bitbank2/CO2_USB_033/User/Open_Sans_Condensed_Bold_24.h

// Created by http://oleddisplay.squix.ch/ Consider a donation
// In case of problems make sure that you are using the font file with the correct version!
const uint8_t Open_Sans_Condensed_Bold_24Bitmaps[] PROGMEM = {

	// Bitmap Data:
	0x00, // ' '
	0x77,0x77,0x77,0x77,0x77,0x70,0x07,0xFF,0x70, // '!'
	0xE7,0x63,0x63,0x63,0x63,0x63, // '"'
	0x0E,0x60,0x63,0x03,0x38,0x19,0xC0,0xCC,0x3F,0xFD,0xFF,0xE3,0x98,0x18,0xC0,0xCE,0x3F,0xFD,0xFF,0xE1,0x98,0x1C,0xC0,0xE6,0x06,0x30,0x33,0x80, // '#'
	0x08,0x04,0x0F,0x8F,0xFF,0xF7,0x4B,0xA1,0xD0,0x78,0x1F,0x03,0xC1,0x70,0xBC,0x5F,0xFF,0xFE,0x7E,0x04,0x02,0x00, // '$'
	0x78,0x30,0xFC,0x30,0xEC,0x70,0xCC,0x60,0xCC,0xE0,0xCE,0xC0,0xCC,0xDE,0xCD,0xFE,0xED,0xB7,0xFF,0xB3,0x7B,0x73,0x03,0x73,0x07,0x73,0x06,0x33,0x0E,0x37,0x0C,0x3E,0x1C,0x1C, // '%'
	0x1E,0x01,0xFC,0x1F,0xE0,0xE7,0x07,0x38,0x3D,0xC0,0xFC,0x03,0xC0,0x7E,0x33,0xF3,0xB9,0xDD,0xCF,0xEE,0x3E,0x70,0xF3,0xFF,0x8F,0xFE,0x3E,0x70, // '&'
	0xE6,0x66,0x66, // '''
	0x1C,0xE3,0x9C,0x71,0xCE,0x38,0xE3,0x8E,0x38,0xE3,0x8E,0x1C,0x71,0xC3,0x8E,0x1C, // '('
	0xE1,0xC7,0x0E,0x38,0xE1,0xC7,0x1C,0x71,0xC7,0x1C,0x71,0xCE,0x38,0xE7,0x1C,0xE0, // ')'
	0x1C,0x0E,0x07,0x1F,0x7F,0xF9,0xF8,0xF8,0xEC,0x77,0x11,0x00, // '*'
	0x1C,0x0E,0x07,0x03,0x8F,0xFF,0xFC,0x70,0x38,0x1C,0x0E,0x07,0x00, // '+'
	0x7F,0xEE,0xEC, // ','
	0xFF,0xFF,0xC0, // '-'
	0x7F,0xF7, // '.'
	0x01,0xC0,0xE0,0x38,0x1C,0x07,0x01,0xC0,0xE0,0x38,0x0E,0x07,0x01,0xC0,0xE0,0x38,0x0E,0x07,0x01,0xC0,0xE0,0x00, // '/'
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
	  {   487,  15,  19,  18,    1,  -17 }, // '@'
	  {   523,  13,  17,  14,    0,  -17 }, // 'A'
	  {   551,  10,  17,  13,    1,  -17 }, // 'B'
	  {   573,  10,  17,  12,    1,  -17 }, // 'C'
	  {   595,  11,  17,  14,    1,  -17 }, // 'D'
	  {   619,   8,  17,  11,    1,  -17 }, // 'E'
	  {   636,   7,  17,  11,    2,  -17 }, // 'F'
	  {   651,  11,  17,  14,    1,  -17 }, // 'G'
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
};
const GFXfont Open_Sans_Condensed_Bold_24 PROGMEM = {
(uint8_t  *)Open_Sans_Condensed_Bold_24Bitmaps,(GFXglyph *)Open_Sans_Condensed_Bold_24Glyphs,0x20, 0x7E, 33};
