bitbank2/CO2_USB_033/User/bb_logo_40x80.h

// Created with image_to_c
// https://github.com/bitbank2/image_to_c
//
// bb_logo_40x80
// Data size = 786 bytes
//
// OS/2 BMP, Compression=None, Size: 40 x 80, 1-Bpp
//
// for non-Arduino builds...
#ifndef PROGMEM
#define PROGMEM
#endif
const uint8_t bb_logo_40x80[] PROGMEM = {
	0xff,0xff,0x83,0xff,0xff,0x00,0x00,0x00,0xff,0xff,0x01,0xff,0xff,0x00,
	0x00,0x00,0xff,0xff,0x38,0xff,0xff,0x00,0x00,0x00,0xff,0xfe,0x3c,0x7f,0xff,0x00,
	0x00,0x00,0xff,0xfe,0x7e,0x7f,0xff,0x00,0x00,0x00,0xff,0xfe,0x7c,0x7f,0xff,0x00,
	0x00,0x00,0xff,0xfe,0x3c,0xff,0xff,0x00,0x00,0x00,0xff,0xff,0x00,0xff,0xff,0x00,
	0x00,0x00,0xff,0xff,0x81,0xff,0xff,0x00,0x00,0x00,0xff,0xff,0xe7,0xff,0xff,0x00,
	0x00,0x00,0xff,0xff,0xe7,0xff,0xff,0x00,0x00,0x00,0xff,0xff,0xe7,0xff,0xff,0x00,
	0x00,0x00,0xff,0xff,0xe7,0xff,0xff,0x00,0x00,0x00,0xff,0xff,0xe7,0xff,0xff,0x00,
	0x00,0x00,0xff,0xff,0xc3,0xff,0xff,0x00,0x00,0x00,0xff,0xfc,0x00,0x3f,0xff,0x00,
	0x00,0x00,0xff,0xf0,0x00,0x0f,0xff,0x00,0x00,0x00,0xff,0xe0,0x00,0x07,0xff,0x00,
	0x00,0x00,0xff,0x80,0x00,0x01,0xff,0x00,0x00,0x00,0xff,0x00,0x00,0x00,0xff,0x00,
	0x00,0x00,0xfe,0x00,0xff,0x00,0x7f,0x00,0x00,0x00,0xfc,0x03,0xff,0xc0,0x3f,0x00,
	0x00,0x00,0xf8,0x0f,0xff,0xf0,0x1f,0x00,0x00,0x00,0xf8,0x0f,0xff,0xf0,0x1f,0x00,
	0x00,0x00,0xf0,0x1f,0xff,0xf8,0x0f,0x00,0x00,0x00,0xf0,0x3f,0xff,0xfc,0x0f,0x00,
	0x00,0x00,0xf0,0x7c,0xff,0x3e,0x0f,0x00,0x00,0x00,0xf0,0xfc,0x7e,0x3f,0x07,0x00,
	0x00,0x00,0xe0,0xfc,0x7e,0x3f,0x07,0x00,0x00,0x00,0xe0,0xfc,0x7e,0x3f,0x07,0x00,
	0x00,0x00,0xe0,0xfc,0x7e,0x3f,0x07,0x00,0x00,0x00,0xe0,0xfc,0xff,0x3f,0x07,0x00,
	0x00,0x00,0xe0,0xff,0xff,0xff,0x07,0x00,0x00,0x00,0xe0,0x7f,0xff,0xfe,0x07,0x00,
	0x00,0x00,0xe0,0x3e,0x01,0xfc,0x07,0x00,0x00,0x00,0xe0,0x00,0x00,0x00,0x07,0x00,
	0x00,0x00,0xe0,0x00,0x00,0x00,0x07,0x00,0x00,0x00,0xe0,0x00,0x00,0x00,0x07,0x00,
	0x00,0x00,0xe0,0x00,0x00,0x00,0x07,0x00,0x00,0x00,0xe0,0x00,0x00,0x00,0x07,0x00,
	0x00,0x00,0xe0,0x00,0x00,0x00,0x07,0x00,0x00,0x00,0xe0,0x0f,0x87,0xe0,0x07,0x00,
	0x00,0x00,0xe0,0x18,0xc6,0x30,0x07,0x00,0x00,0x00,0xe0,0x18,0x66,0x30,0x07,0x00,
	0x00,0x00,0xe0,0x18,0x66,0x30,0x07,0x00,0x00,0x00,0xe0,0x18,0xc6,0x60,0x07,0x00,
	0x00,0x00,0xe0,0x1f,0x87,0xc0,0x07,0x00,0x00,0x00,0xe0,0x1f,0xc7,0xf0,0x07,0x00,
	0x00,0x00,0xe0,0x18,0xc6,0x30,0x07,0x00,0x00,0x00,0xe0,0x18,0x66,0x18,0x07,0x00,
	0x00,0x00,0xe0,0x18,0x66,0x18,0x07,0x00,0x00,0x00,0xe0,0x18,0x66,0x18,0x07,0x00,
	0x00,0x00,0xe0,0x18,0xc6,0x30,0x07,0x00,0x00,0x00,0xe0,0x0f,0x83,0xe0,0x07,0x00,
	0x00,0x00,0xe0,0x00,0x00,0x00,0x07,0x00,0x00,0x00,0xe0,0x00,0x00,0x00,0x07,0x00,
	0x00,0x00,0xe0,0x00,0x00,0x00,0x07,0x00,0x00,0x00,0xe0,0x00,0x00,0x00,0x07,0x00,
	0x00,0x00,0xe0,0x00,0x00,0x00,0x07,0x00,0x00,0x00,0xe0,0x00,0x00,0x00,0x07,0x00,
	0x00,0x00,0xff,0xff,0xff,0xff,0xff,0x00,0x00,0x00,0xff,0xff,0xff,0xff,0xff,0x00,
	0x00,0x00,0xe0,0x00,0x00,0x00,0x07,0x00,0x00,0x00,0xe0,0x00,0x00,0x00,0x07,0x00,
	0x00,0x00,0xe0,0x00,0x00,0x00,0x07,0x00,0x00,0x00,0xf0,0x00,0x00,0x00,0x0f,0x00,
	0x00,0x00,0xff,0xc0,0xff,0x03,0xff,0x00,0x00,0x00,0xff,0xc0,0xff,0x03,0xff,0x00,
	0x00,0x00,0xff,0xc0,0xff,0x03,0xff,0x00,0x00,0x00,0xff,0xc0,0xff,0x03,0xff,0x00,
	0x00,0x00,0xff,0xc0,0xff,0x03,0xff,0x00,0x00,0x00,0xff,0xc0,0xff,0x03,0xff,0x00,
	0x00,0x00,0xff,0xc0,0x7f,0x03,0xff,0x00,0x00,0x00,0xff,0x80,0x3c,0x00,0xff,0x00,
	0x00,0x00,0xfe,0x00,0x38,0x00,0xff,0x00,0x00,0x00,0xfe,0x00,0x10,0x00,0x7f,0x00,
	0x00,0x00,0xfe,0x00,0x10,0x00,0x7f,0x00,0x00,0x00,0xfe,0x00,0x10,0x00,0x7f,0x00,
	0x00,0x00,0xfe,0x00,0x10,0x00,0xff,0x00,0x00,0x00,0xff,0x80,0x38,0x00,0xff,0x00,
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
