bitbank2/CO2_USB_033/User/battery.h

//
// batt_charging
// Data size = 64 bytes
//
const uint8_t battchg_32x16[] = {
    0xe0,0x00,0x00,0x00,0xcf,0xff,0xff,0xfe,0xdf,0xff,0xff,0xfe,0xdf,0xf9,0x9f,0xfe,
	0x9f,0xf9,0x9f,0xfe,0x3f,0xf9,0x9f,0xfe,0x7f,0xf9,0x9f,0xfe,0x7f,0xf0,0x0f,0xfe,
	0x7f,0xf0,0x0f,0xfe,0x7f,0xf0,0x0f,0xfe,0x3f,0xf8,0x1f,0xfe,0x9f,0xfe,0x7f,0xfe,
	0xdf,0xfe,0x7f,0xfe,0xdf,0xfe,0x7f,0xfe,0xcf,0xff,0xff,0xfe,0xe0,0x00,0x00,0x00};
//
// batt100_32x16
// Data size = 64 bytes
//
const uint8_t batt100_32x16[] = {
	0xe0,0x00,0x00,0x00,0xcf,0xff,0xff,0xfe,0xdf,0xff,0xff,0xfe,0xdc,0x10,0x41,0x06,
	0x9c,0x10,0x41,0x06,0x3c,0x10,0x41,0x06,0x7c,0x10,0x41,0x06,0x7c,0x10,0x41,0x06,
	0x7c,0x10,0x41,0x06,0x7c,0x10,0x41,0x06,0x3c,0x10,0x41,0x06,0x9c,0x10,0x41,0x06,
	0xdc,0x10,0x41,0x06,0xdf,0xff,0xff,0xfe,0xcf,0xff,0xff,0xfe,0xe0,0x00,0x00,0x00};
//
// batt75_32x16
// Data size = 64 bytes
//
const uint8_t batt75_32x16[] = {
	0xe0,0x00,0x00,0x00,0xcf,0xff,0xff,0xfe,0xdf,0xff,0xff,0xfe,0xdf,0xf0,0x41,0x06,
	0x9f,0xf0,0x41,0x06,0x3f,0xf0,0x41,0x06,0x7f,0xf0,0x41,0x06,0x7f,0xf0,0x41,0x06,
	0x7f,0xf0,0x41,0x06,0x7f,0xf0,0x41,0x06,0x3f,0xf0,0x41,0x06,0x9f,0xf0,0x41,0x06,
	0xdf,0xf0,0x41,0x06,0xdf,0xff,0xff,0xfe,0xcf,0xff,0xff,0xfe,0xe0,0x00,0x00,0x00};
//
// batt50_32x16
// Data size = 64 bytes
//
const uint8_t batt50_32x16[] = {
	0xe0,0x00,0x00,0x00,0xcf,0xff,0xff,0xfe,0xdf,0xff,0xff,0xfe,0xdf,0xff,0xc1,0x06,
	0x9f,0xff,0xc1,0x06,0x3f,0xff,0xc1,0x06,0x7f,0xff,0xc1,0x06,0x7f,0xff,0xc1,0x06,
	0x7f,0xff,0xc1,0x06,0x7f,0xff,0xc1,0x06,0x3f,0xff,0xc1,0x06,0x9f,0xff,0xc1,0x06,
	0xdf,0xff,0xc1,0x06,0xdf,0xff,0xff,0xfe,0xcf,0xff,0xff,0xfe,0xe0,0x00,0x00,0x00};
//
// batt25_32x16
// Data size = 64 bytes
//
const uint8_t batt25_32x16[] = {
	0xe0,0x00,0x00,0x00,0xcf,0xff,0xff,0xfe,0xdf,0xff,0xff,0xfe,0xdf,0xff,0xff,0x06,
	0x9f,0xff,0xff,0x06,0x3f,0xff,0xff,0x06,0x7f,0xff,0xff,0x06,0x7f,0xff,0xff,0x06,
	0x7f,0xff,0xff,0x06,0x7f,0xff,0xff,0x06,0x3f,0xff,0xff,0x06,0x9f,0xff,0xff,0x06,
	0xdf,0xff,0xff,0x06,0xdf,0xff,0xff,0xfe,0xcf,0xff,0xff,0xfe,0xe0,0x00,0x00,0x00};
//
// batt0_32x16
// Data size = 64 bytes
//
const uint8_t batt0_32x16[] = {
	0xe0,0x00,0x00,0x00,0xcf,0xff,0xff,0xfe,0xdf,0xfe,0x3f,0xfe,0xdf,0xfe,0x3f,0xfe,
	0x9f,0xfe,0x3f,0xfe,0x3f,0xff,0xff,0xfe,0x7f,0xfe,0x3f,0xfe,0x7f,0xfc,0x1f,0xfe,
	0x7f,0xfc,0x1f,0xfe,0x7f,0xfc,0x1f,0xfe,0x3f,0xfc,0x1f,0xfe,0x9f,0xfc,0x1f,0xfe,
	0xdf,0xfc,0x1f,0xfe,0xdf,0xfe,0x3f,0xfe,0xcf,0xff,0xff,0xfe,0xe0,0x00,0x00,0x00};
